johanwheeler/ch32-fireplace/Graphics/Front_silks.png

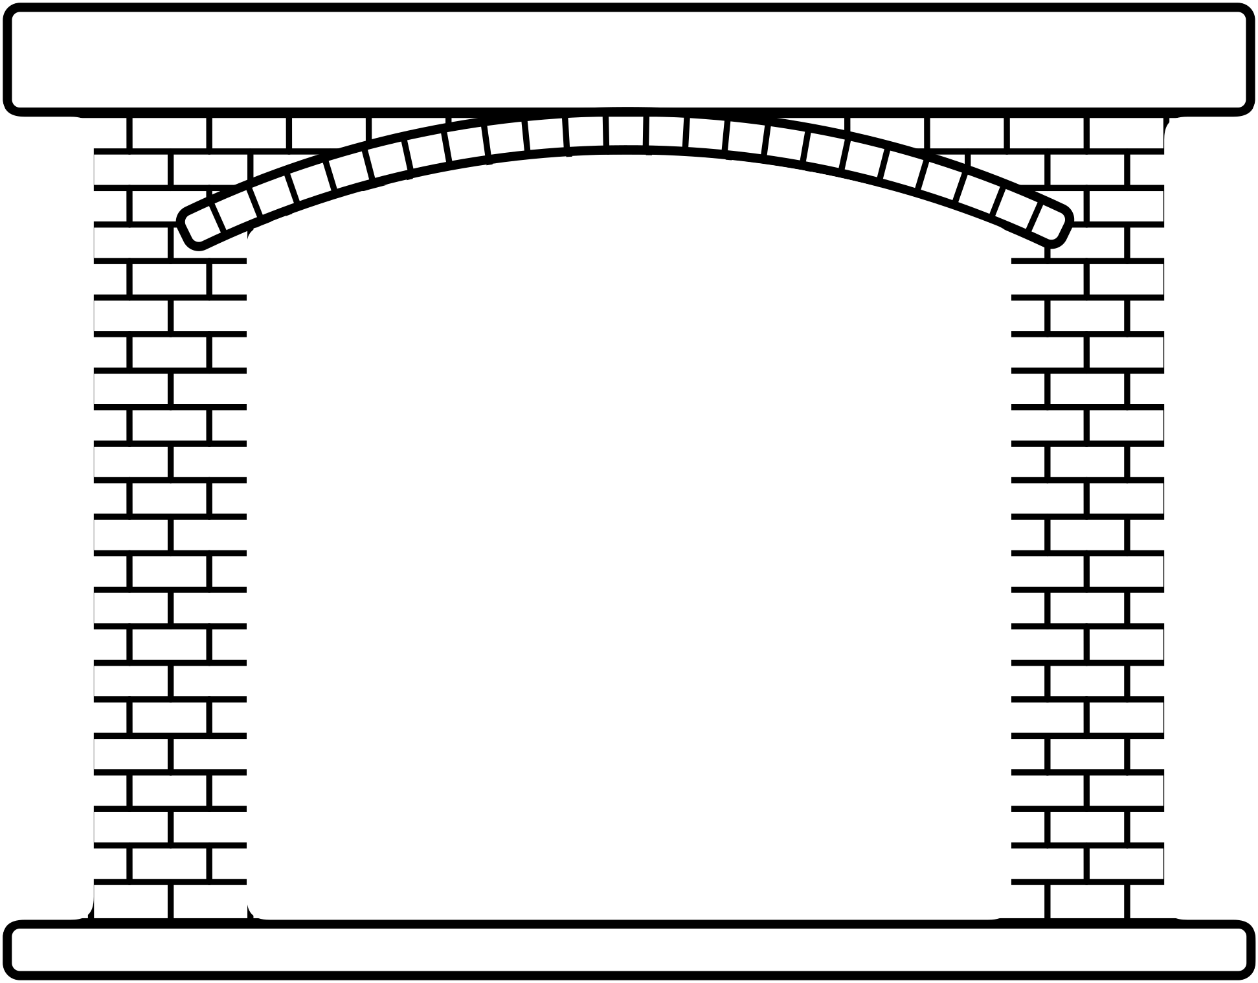
Graphics/Front_silks.png
