johanwheeler/ch32-fireplace/Graphics/Middle_silks.png

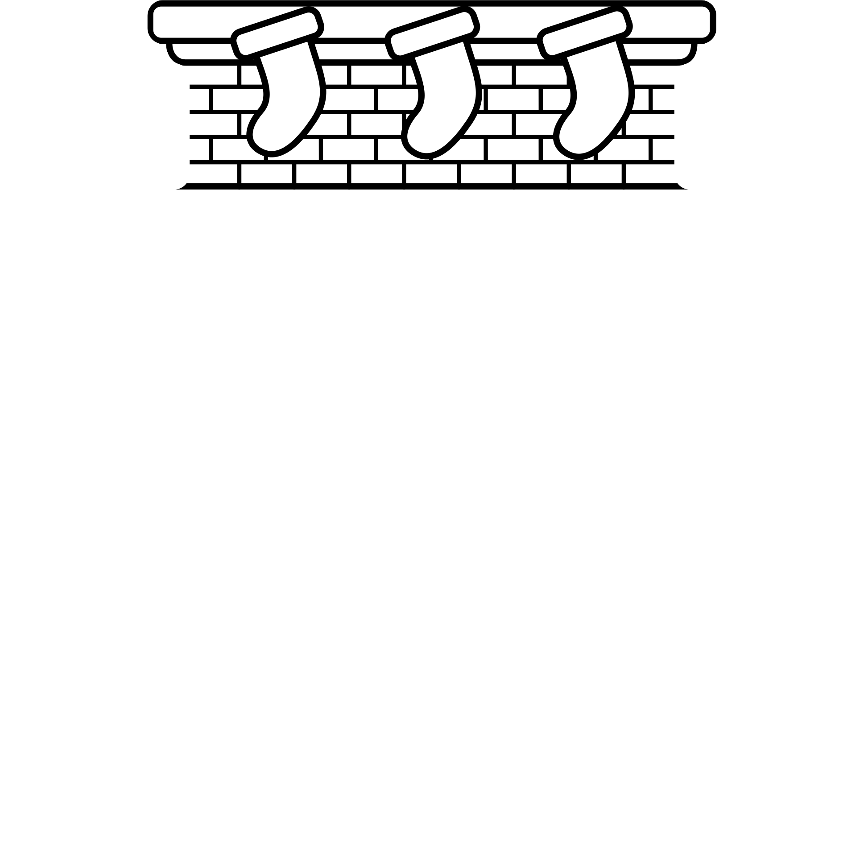
Graphics/Middle_silks.png
