johanwheeler/ch32-fireplace/Media/Finished.jpg

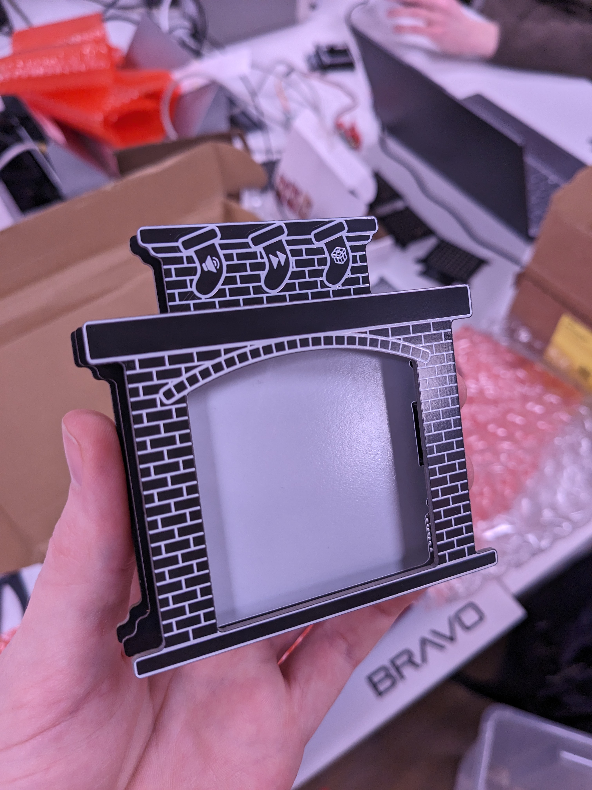
Media/Finished.jpg
