johanwheeler/ch32-fireplace/Media/Many_finished.jpg

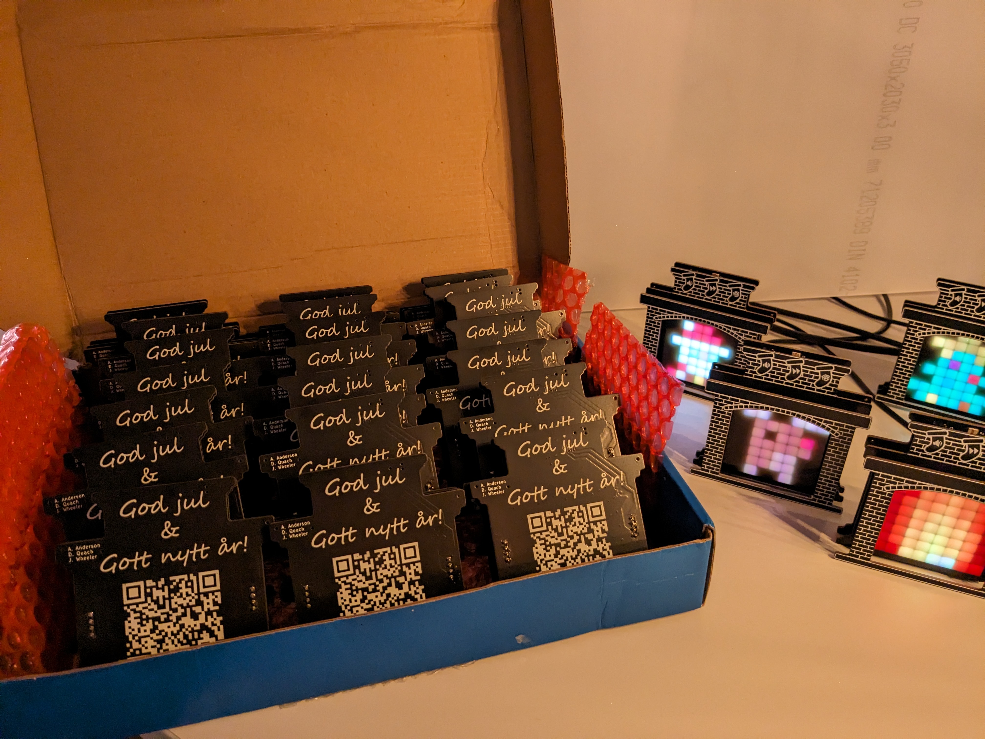
Media/Many_finished.jpg
