johanwheeler/ch32-fireplace/CAD/3D/pogo_block_printmf.3mf

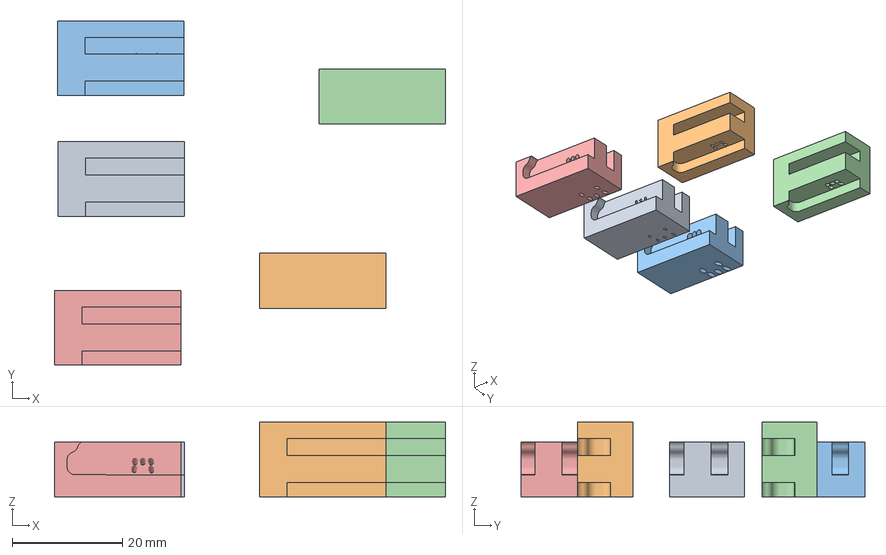
[picture p27: CAD file, 2023-12-10]
CAD/3D/pogo_block_printmf.3mf
71.0 x 62.5 x 13.6 mm
pogo_block_0
pogo_block_0.1
pogo_block_0.4
pogo_block_0.3
pogo_block_0.2
