johanwheeler/ch32-fireplace/CAD/DXF/usb-c-cutout.dxf

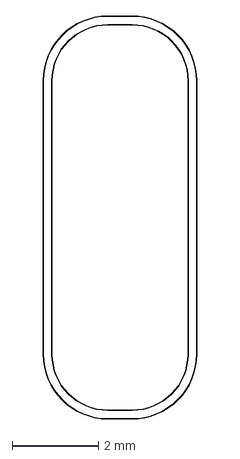
[picture p28: CAD file, 2023-11-05]
CAD/DXF/usb-c-cutout.dxf
3.56 x 9.34 mm
