johanwheeler/ch32-fireplace/Graphics/Back.dxf

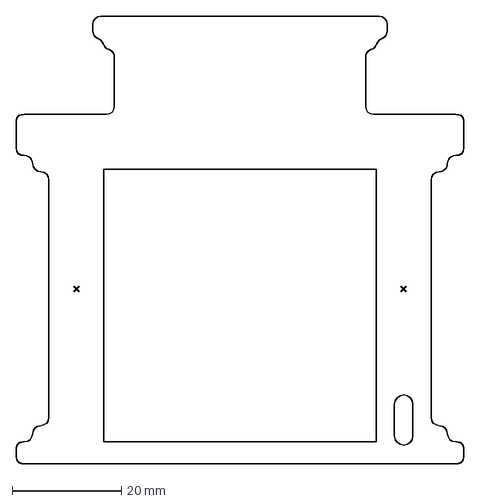
[picture p29: CAD file, 2023-10-28]
Graphics/Back.dxf
82.0 x 82.0 mm
