johanwheeler/ch32-fireplace/CAD/DXF/front.dxf

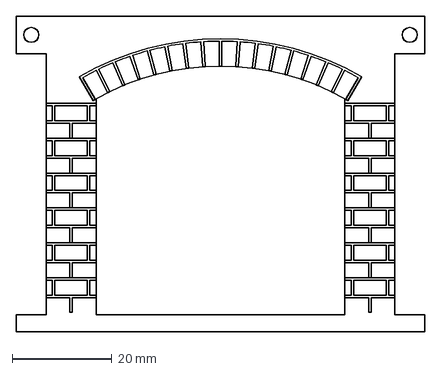
[picture p30: CAD file, 2023-11-05]
CAD/DXF/front.dxf
82.0 x 63.4 mm
