johanwheeler/ch32-fireplace/Graphics/Front.dxf

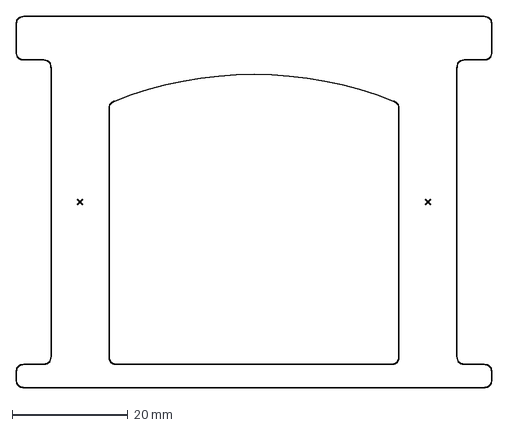
[picture p31: CAD file, 2023-10-28]
Graphics/Front.dxf
82.0 x 64.0 mm
