johanwheeler/ch32-fireplace/CAD/3D/pinHeaderJig_v4.3mf

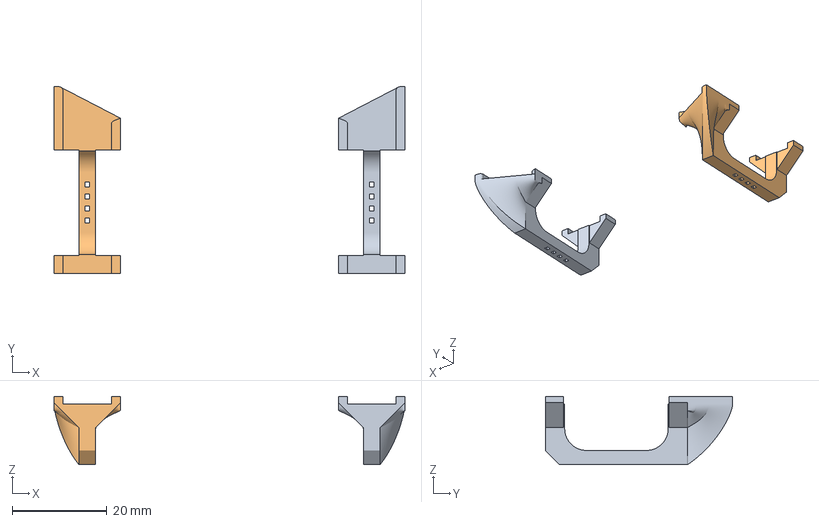
[picture p32: CAD file, 2023-12-09]
CAD/3D/pinHeaderJig_v4.3mf
74.0 x 39.5 x 14.4 mm
