johanwheeler/ch32-fireplace/CAD/3D/Grid_v3.1_print3mf.3mf

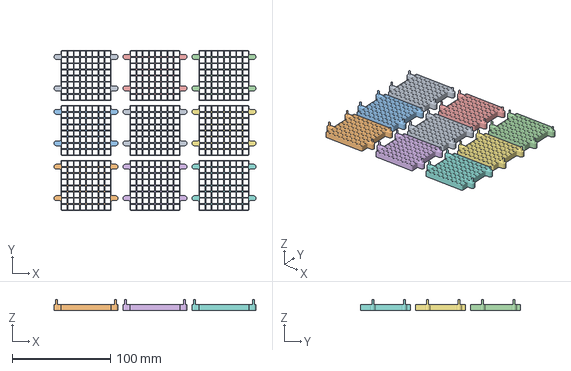
[picture p33: CAD file, 2023-12-09]
CAD/3D/Grid_v3.1_print3mf.3mf
205.2 x 162.4 x 11.5 mm
