johanwheeler/ch32-fireplace/CAD/3D/pinHeaderJig_v4_print.3mf

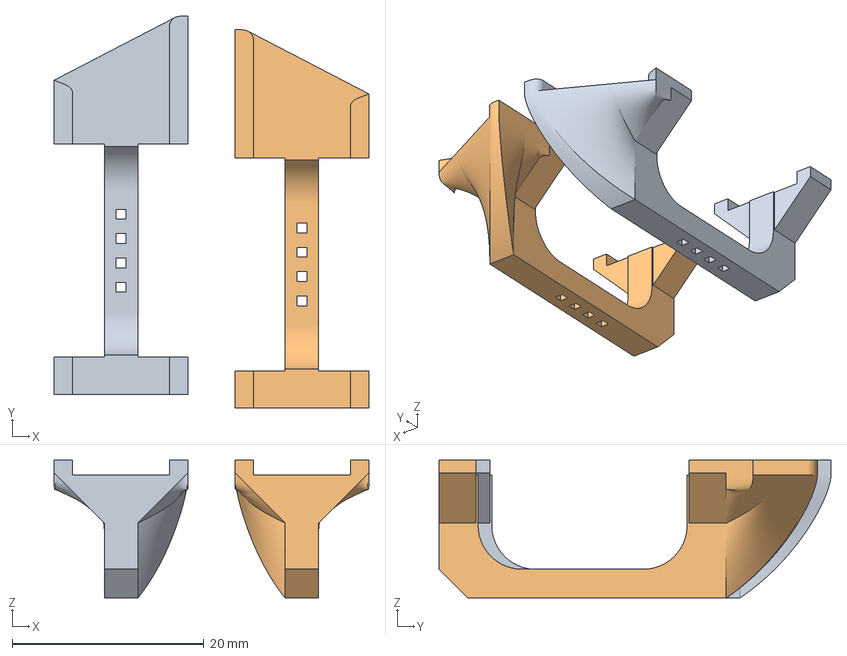
[picture p34: CAD file, 2023-12-09]
CAD/3D/pinHeaderJig_v4_print.3mf
32.9 x 40.9 x 14.4 mm
