johanwheeler/ch32-fireplace/CAD/3D/blablab.3mf

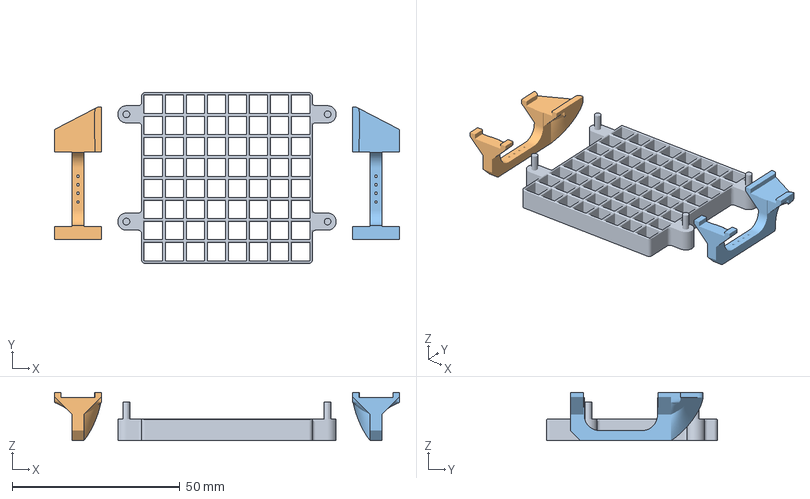
[picture p36: CAD file, 2023-12-09]
CAD/3D/blablab.3mf
102.9 x 50.9 x 14.4 mm
Grid_v3.1_6.5mm_high
