johanwheeler/ch32-fireplace/CAD/3D/Grid_v3.1_6.5mm_high.3mf

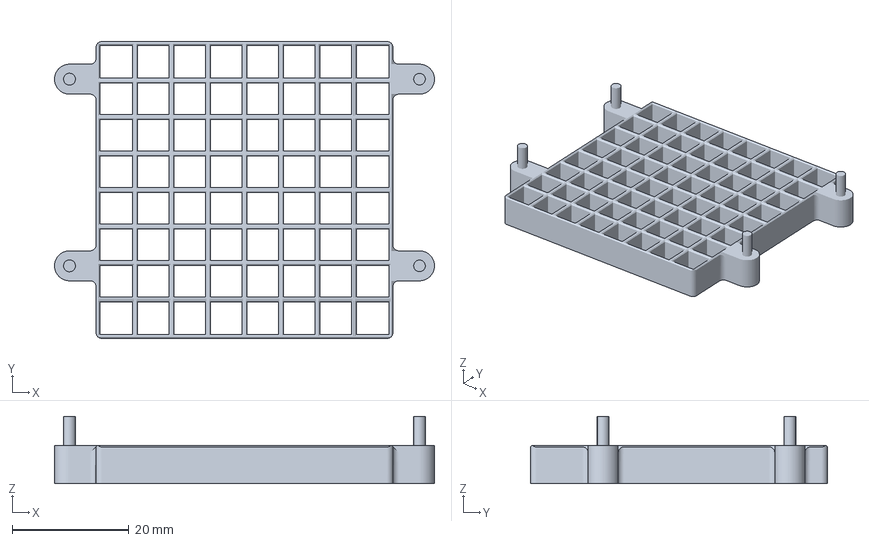
[picture p37: CAD file, 2023-12-09]
CAD/3D/Grid_v3.1_6.5mm_high.3mf
65.1 x 50.9 x 11.5 mm
