johanwheeler/ch32-fireplace/CAD/3D/Grid_v3.0_print.3mf

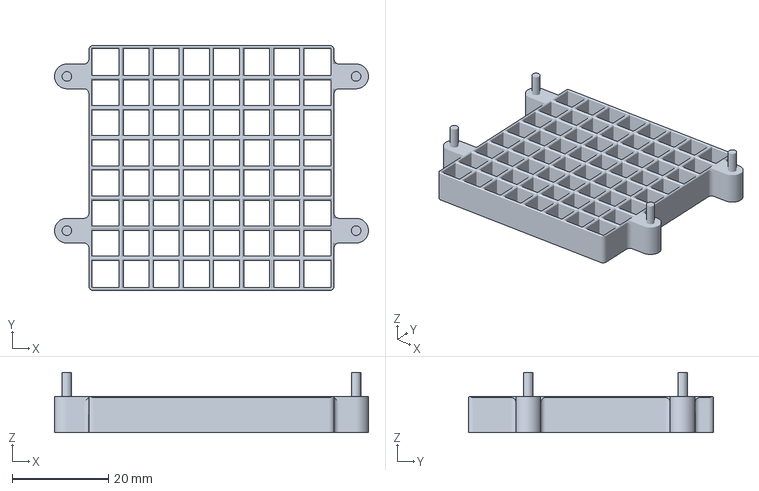
[picture p38: CAD file, 2023-12-05]
CAD/3D/Grid_v3.0_print.3mf
65.1 x 50.9 x 12.5 mm
