johanwheeler/ch32-fireplace/CAD/3D/1.5mm led grid.stl

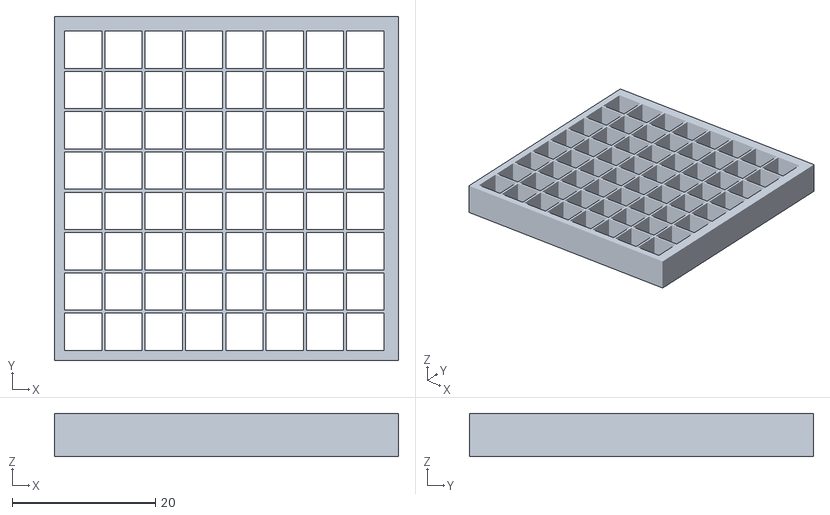
[picture p40: CAD file, 2023-11-04]
CAD/3D/1.5mm led grid.stl
48.0 x 48.0 x 6.00
