johanwheeler/ch32-fireplace/CAD/3D/female_pin_header.step

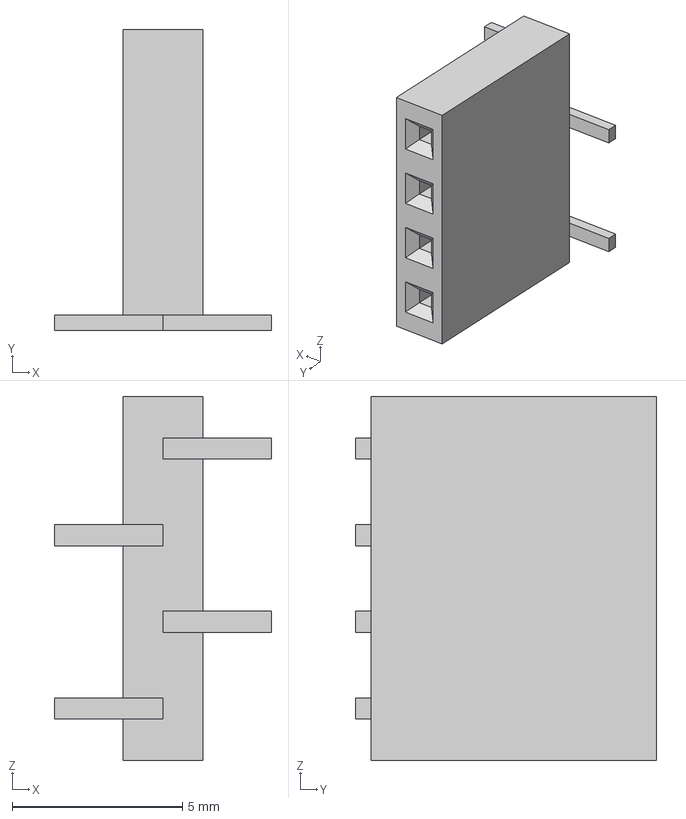
[picture p41: CAD file, 2023-11-04]
CAD/3D/female_pin_header.step
6.38 x 8.82 x 10.7 mm
