johanwheeler/ch32-fireplace/CAD/3D/buzzer_C391038.step

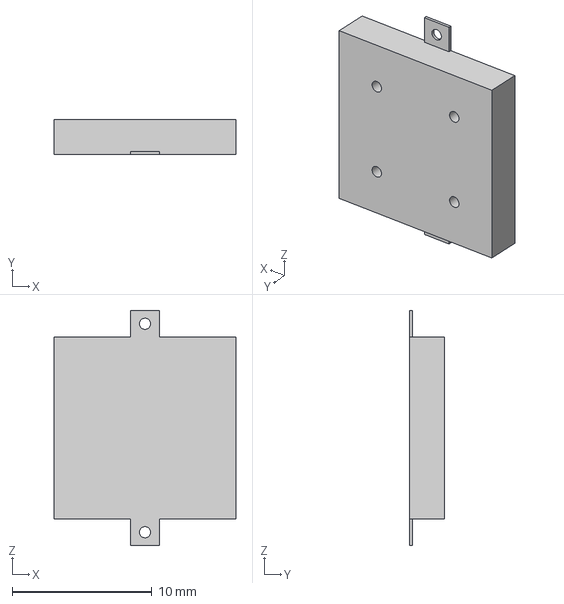
[picture p42: CAD file, 2023-11-04]
CAD/3D/buzzer_C391038.step
13.0 x 2.50 x 16.8 mm
