johanwheeler/ch32-fireplace/CAD/3D/photo_GT36528.step

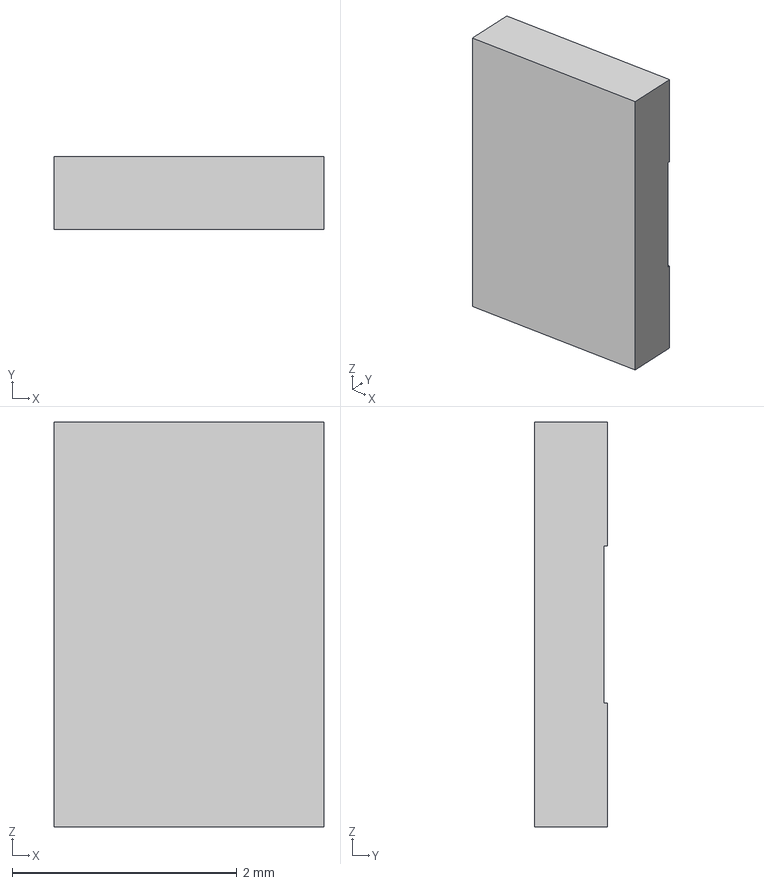
[picture p43: CAD file, 2023-11-04]
CAD/3D/photo_GT36528.step
2.40 x 0.65 x 3.60 mm
