johanwheeler/ch32-fireplace/CAD/3D/led_C191KRKT.step

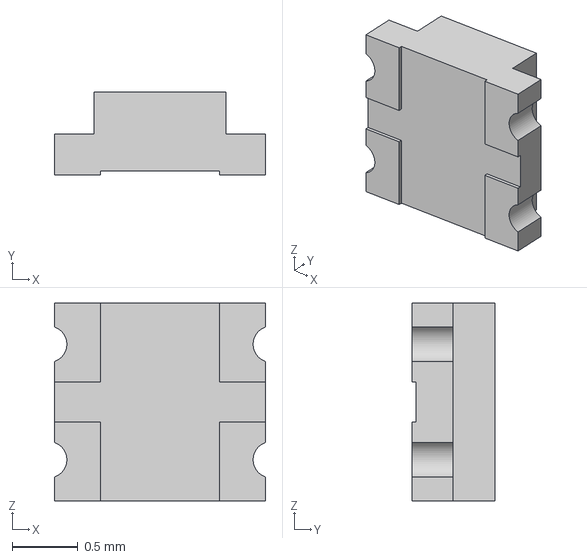
[picture p44: CAD file, 2023-11-04]
CAD/3D/led_C191KRKT.step
1.60 x 0.63 x 1.50 mm
