johanwheeler/ch32-fireplace/CAD/3D/footprint_test v2.step

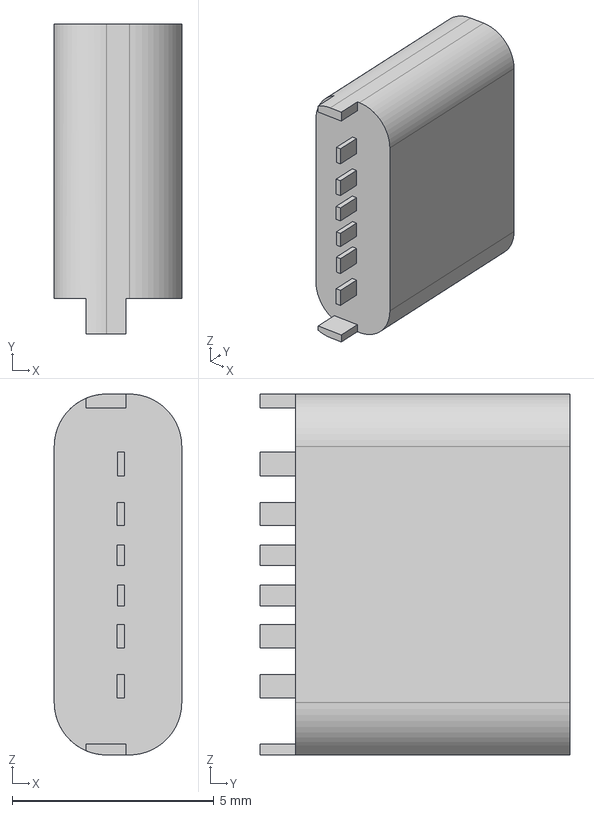
[picture p45: CAD file, 2023-10-28]
CAD/3D/footprint_test v2.step
3.16 x 7.68 x 8.94 mm
