johanwheeler/ch32-fireplace/Media/Back_soldered.jpg

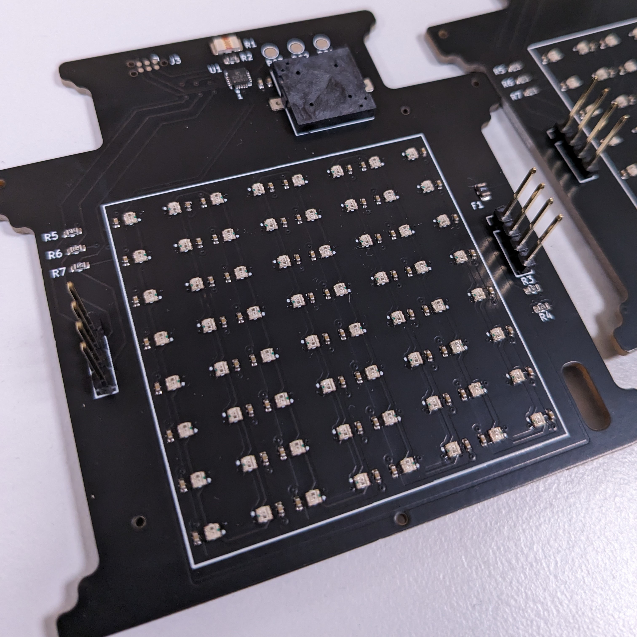
Media/Back_soldered.jpg
