johanwheeler/ch32-fireplace/Media/Mid_soldering.JPG

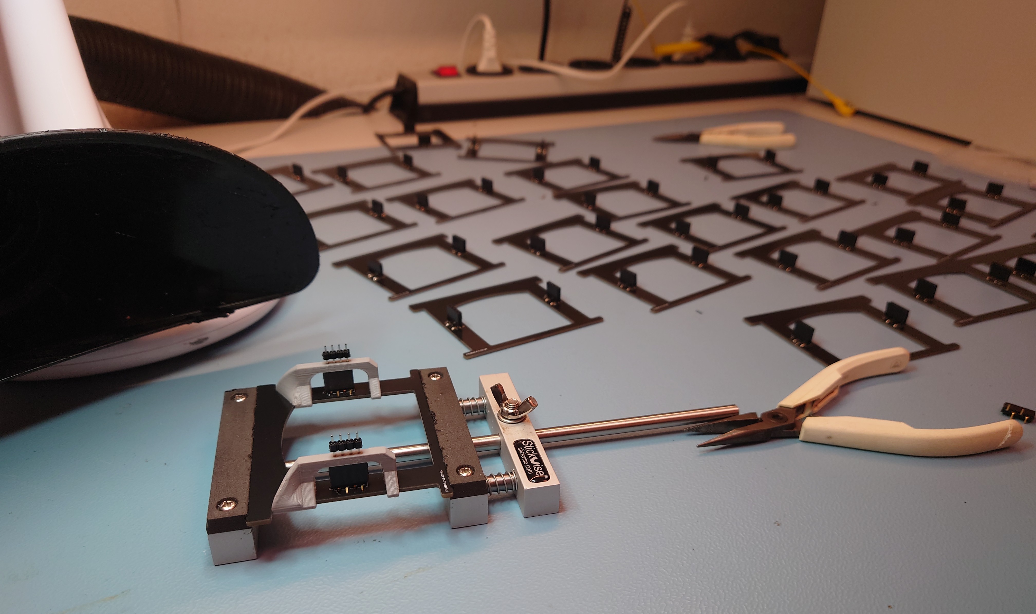
Media/Mid_soldering.JPG
