johanwheeler/ch32-fireplace/Media/Soldering_mid.jpg

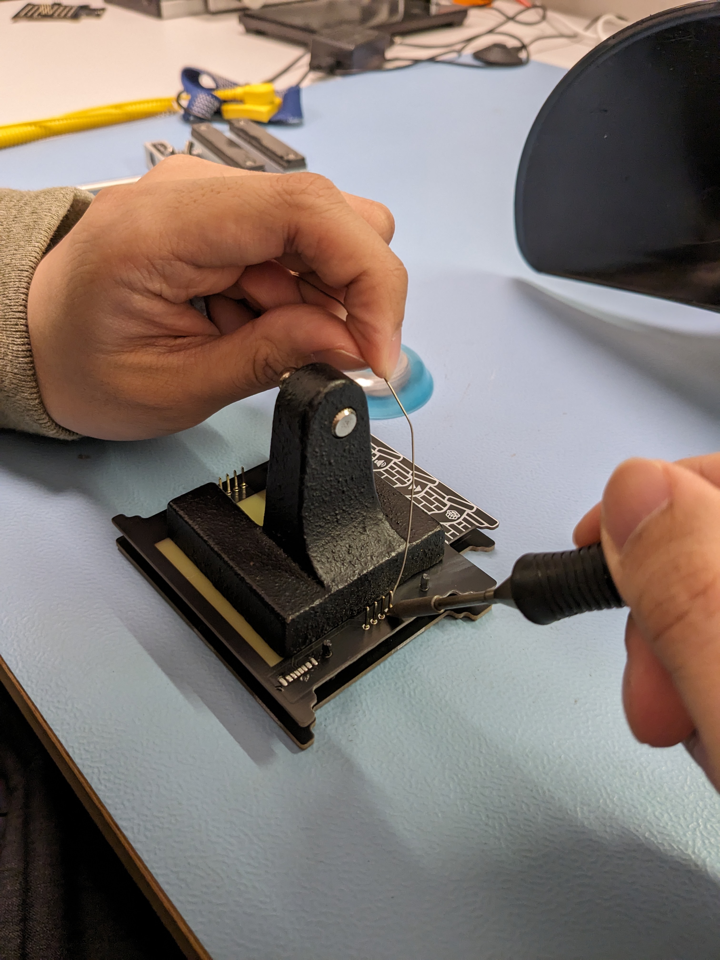
Media/Soldering_mid.jpg
