johanwheeler/ch32-fireplace/SW/fireplace-PIO/src/funconfig.h

#ifndef _FUNCONFIG_H
#define _FUNCONFIG_H

#define CH32V003 1

#define FUNCONF_SYSTICK_USE_HCLK 1
#define FUNCONF_USE_DEBUGPRINTF 0
#define FUNCONF_USE_UARTPRINTF 1
#define FUNCONF_UART_PRINTF_BAUD 115200

// Project specific defines

#define SCREEN_GPIO_PORT GPIOD
#define SCREEN_GPIO_PIN 0

#endif
